MOSH-Insa-Toulouse/PROJET_CAPTEUR_BARASZ_CHOURY/KiCad/Encodeur Rotatoir/empreinte_encodeur.png

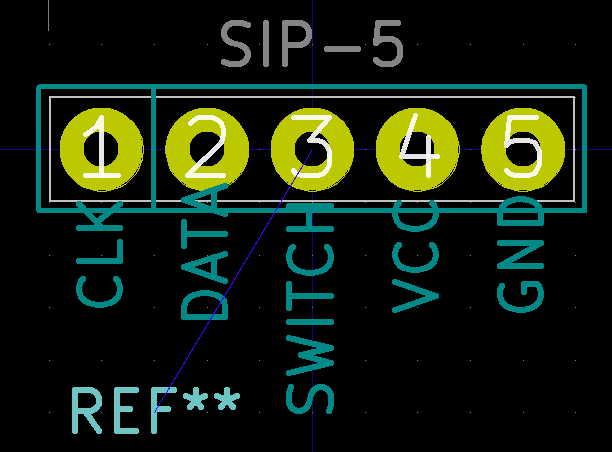
KiCad/Encodeur Rotatoir/empreinte_encodeur.png
