MOSH-Insa-Toulouse/PROJET_CAPTEUR_BARASZ_CHOURY/KiCad/LTC1050/empreinte_LTC1050.png

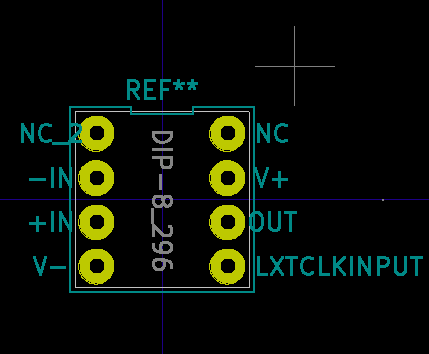
KiCad/LTC1050/empreinte_LTC1050.png
