MOSH-Insa-Toulouse/PROJET_CAPTEUR_BARASZ_CHOURY/KiCad/LTC1050/schema_LTC1050.png

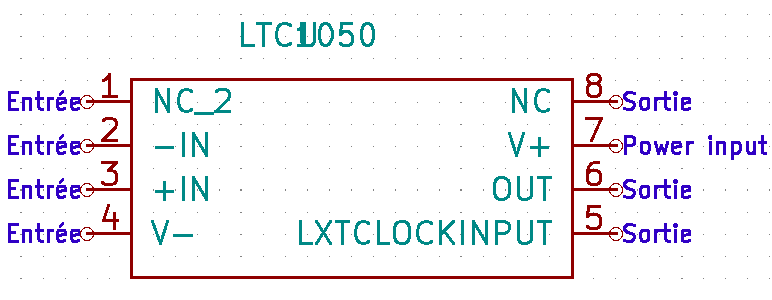
KiCad/LTC1050/schema_LTC1050.png
