MOSH-Insa-Toulouse/PROJET_CAPTEUR_BARASZ_CHOURY/KiCad/Module bluetooth/shema_module_BT.png

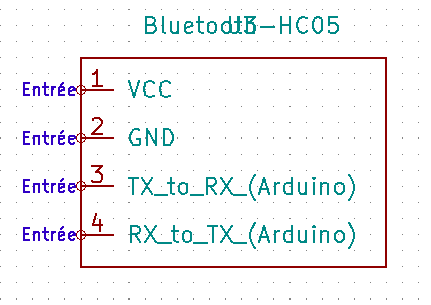
KiCad/Module bluetooth/shema_module_BT.png
