MOSH-Insa-Toulouse/PROJET_CAPTEUR_BARASZ_CHOURY/KiCad/OLED/schema_OLED.png

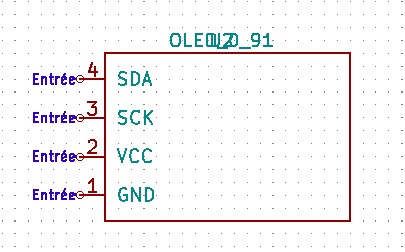
KiCad/OLED/schema_OLED.png
